AndrewWoollett/AVC-Team-B-_or_bust/Design/Images/0001.jpg

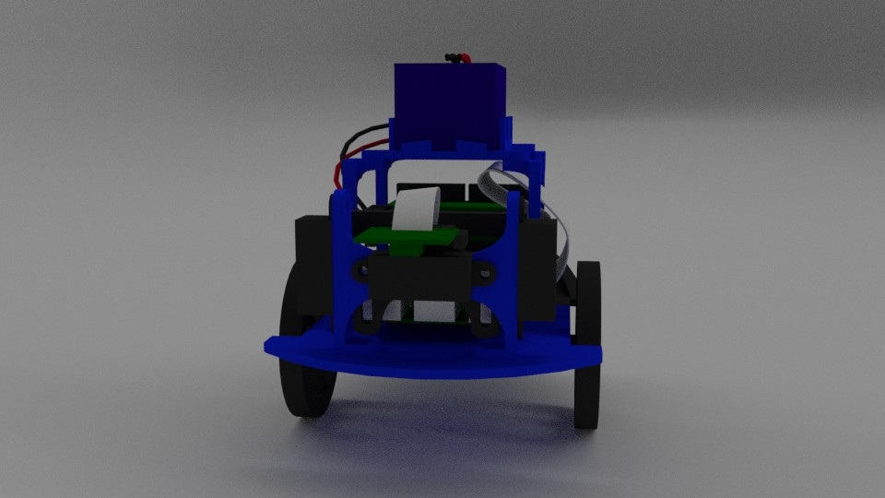
Design/Images/0001.jpg
