AndrewWoollett/AVC-Team-B-_or_bust/Design/Images/0002.jpg

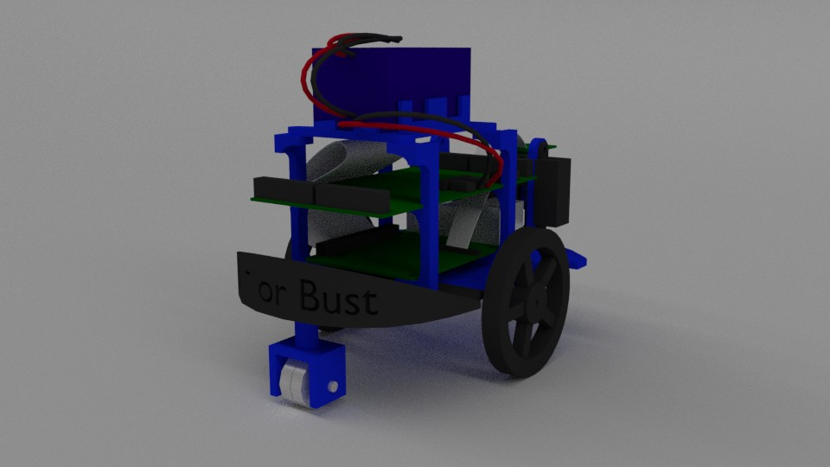
Design/Images/0002.jpg
