AndrewWoollett/AVC-Team-B-_or_bust/Design/Images/0003.jpg

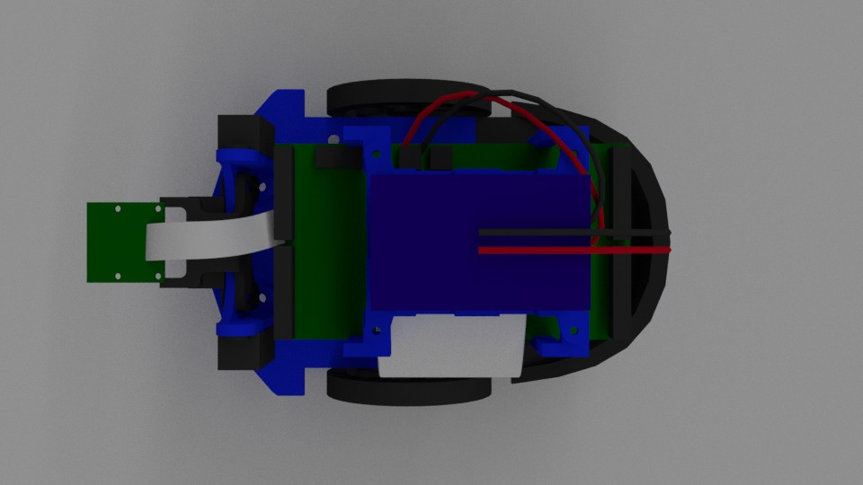
Design/Images/0003.jpg
