AndrewWoollett/AVC-Team-B-_or_bust/Design/Images/0004.jpg

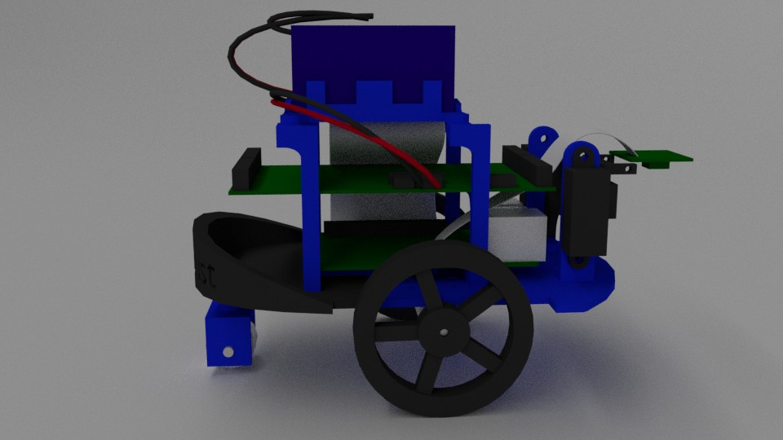
Design/Images/0004.jpg
