AndrewWoollett/AVC-Team-B-_or_bust/Design/Images/angle.jpg

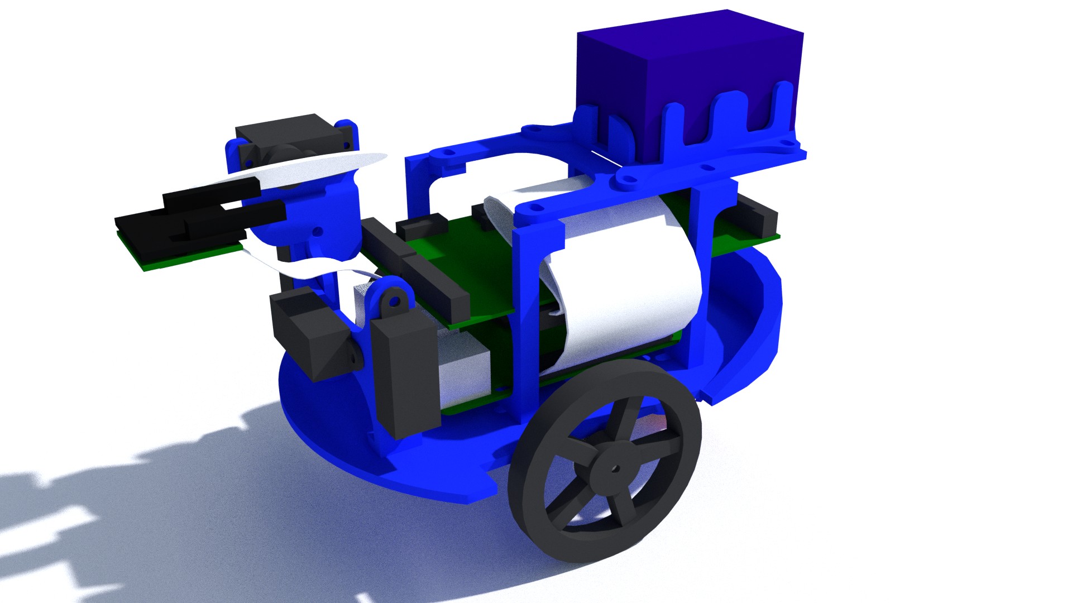
Design/Images/angle.jpg
