AndrewWoollett/AVC-Team-B-_or_bust/Design/Images/Exploded Views/Exploded 1.jpg

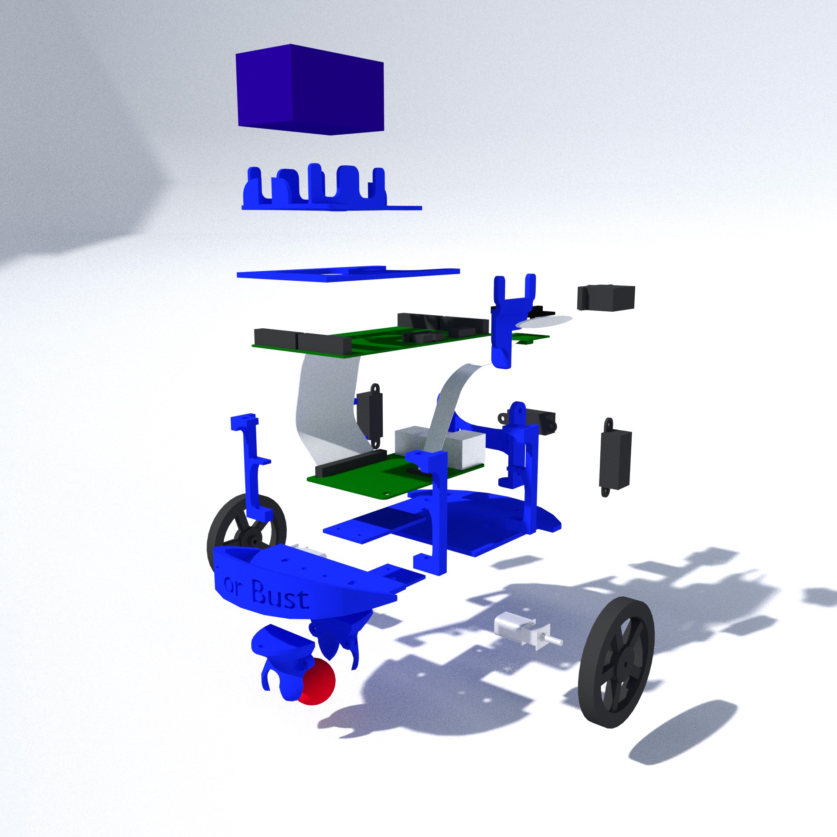
Design/Images/Exploded Views/Exploded 1.jpg
