AndrewWoollett/AVC-Team-B-_or_bust/Design/Images/Exploded Views/Exploded 2.jpg

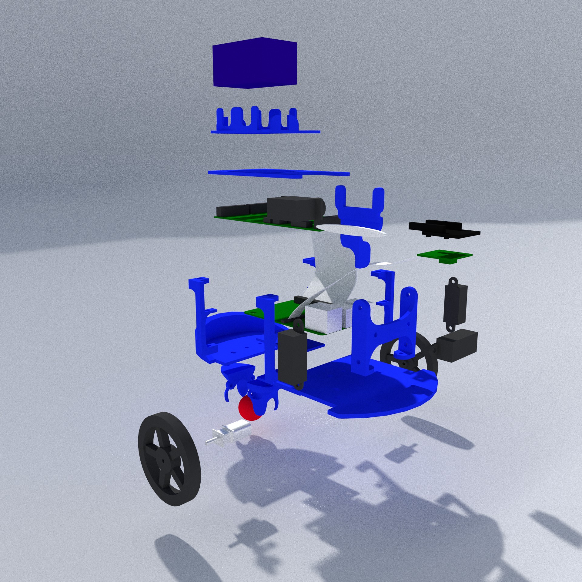
Design/Images/Exploded Views/Exploded 2.jpg
