AndrewWoollett/AVC-Team-B-_or_bust/Design/Images/Exploded Views/Exploded Front.jpg

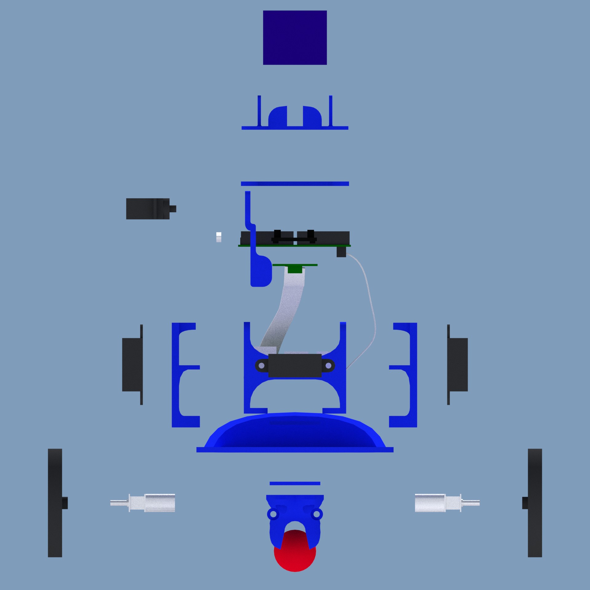
Design/Images/Exploded Views/Exploded Front.jpg
