AndrewWoollett/AVC-Team-B-_or_bust/Design/Images/Exploded Views/Exploded Side.jpg

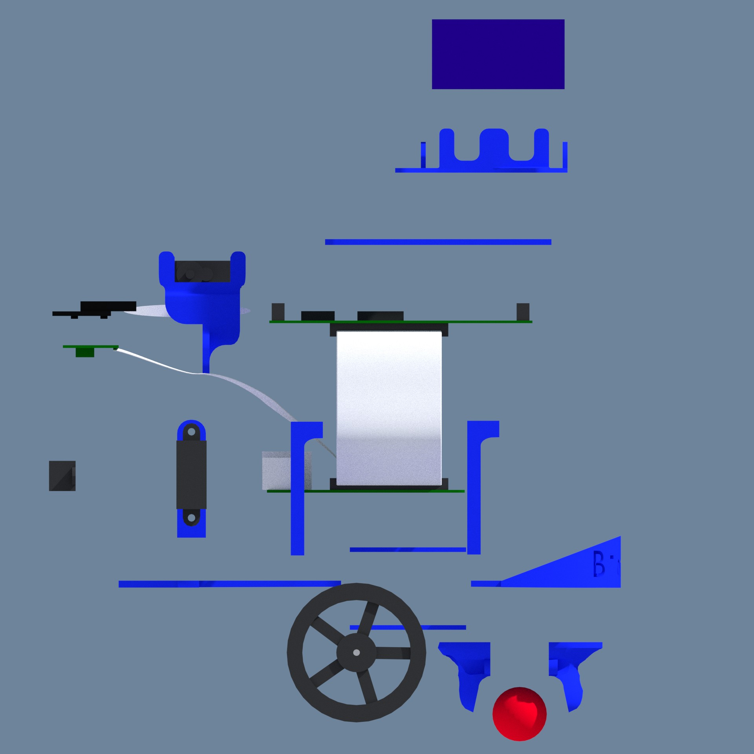
Design/Images/Exploded Views/Exploded Side.jpg
