AndrewWoollett/AVC-Team-B-_or_bust/Design/BaseBack.stl

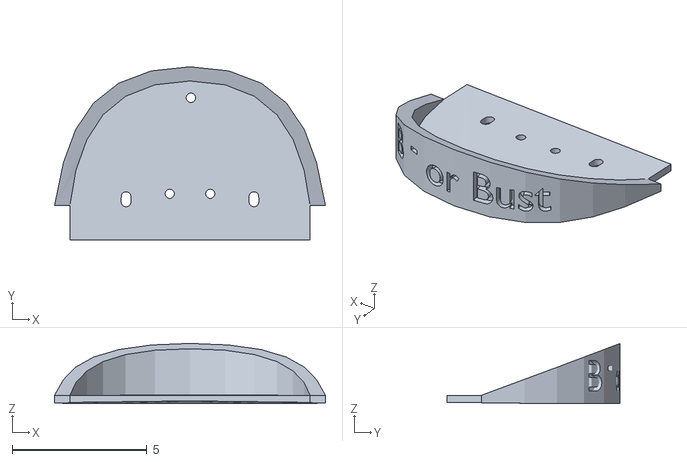
[picture p33: CAD file, 2016-06-08]
Design/BaseBack.stl
10.1 x 6.44 x 2.23
